lab11/buckler/software/apps/analog_accelerometer/README.md

Analog Accelerometer App
========================

Reads data from the [ADXL327](http://www.analog.com/media/en/technical-documentation/data-sheets/ADXL327.pdf)
analog accelerometer. To see output run `make rtt`

nRF SAADC (Successive Approximation Analog to Digital Converter) [API documentation]( https://infocenter.nordicsemi.com/index.jsp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)
