lab11/buckler/software/apps/blink/README.md

Blink
=====

Blinks the LEDs on Buckler

nRF GPIOTE (General Purpose I/O Task/Event) [API documentation](https://infocenter.nordicsemi.com/topic/com.nordic.infocenter.sdk5.v15.1.0/group__nrfx__gpiote.html)
