lab11/buckler/software/apps/sd_card/README.md

SD Card
=======

Writes sample lines to the SD card on Buckler
