lab11/buckler/software/apps/kobukiSquareIMU/README.md

Kobuki Square IMU
=================

Make the [Kobuki](http://kobuki.yujinrobot.com/wiki/online-user-guide/)
drive in a square using the external IMU on the buckler board
