lab11/buckler/software/apps/kobukiSensor/README.md

Kobuki Sensor
=============

Print all of the [Kobuki](http://kobuki.yujinrobot.com/wiki/online-user-guide/)
sensor values
