lab11/buckler/software/apps/button_and_switch/README.md

Buttons App
===========

Use a button and a switch to control LEDs
