lab11/buckler/software/apps/ble_robot_adv/states.h

/*
 * states.h
 *
 *  Created on: Sep 22, 2018
 *      Author: shromonaghosh
 */

#ifndef STATES_H_
#define STATES_H_

#include <stdio.h>

typedef enum {
    OFF=0,
    DRIVING,
} states;

#endif /* STATES_H_ */
