lab11/buckler/software/apps/ble_adv_listen_template/main.c

// BLE RX app
//
// Receives BLE advertisements with data

#include <stdbool.h>
#include <stdint.h>
#include "nrf.h"
#include "app_util.h"
#include "nrf_log.h"
#include "nrf_log_ctrl.h"
#include "nrf_log_default_backends.h"

#include "simple_ble.h"

// BLE configuration
// This is mostly irrelevant since we are scanning only
static simple_ble_config_t ble_config = {
        // BLE address is c0:98:e5:49:00:00
        .platform_id       = 0x49,    // used as 4th octet in device BLE address
        .device_id         = 0x0000,  // Last two octets of device address
        .adv_name          = "EE149", // irrelevant in this example
        .adv_interval      = MSEC_TO_UNITS(1000, UNIT_0_625_MS), // send a packet once per second (minimum is 20 ms)
        .min_conn_interval = MSEC_TO_UNITS(500, UNIT_1_25_MS), // irrelevant if advertising only
        .max_conn_interval = MSEC_TO_UNITS(1000, UNIT_1_25_MS), // irrelevant if advertising only
};
simple_ble_app_t* simple_ble_app;

void ble_evt_adv_report(ble_evt_t const* p_ble_evt) {

  ble_gap_evt_adv_report_t const* adv_report = &(p_ble_evt->evt.gap_evt.params.adv_report);
  // TODO: extract the fields we care about (Peer address and data)

  // TODO: filter on Peer address
  if (false) { // replace with condition on peer address
    // if address matches C0:98:E5:49:FF:FD, loop until we find field 0xFF
    while (1) {
      // TODO: get length of field
      // TODO: get type of field: if type is 0xFF, we found it!
      // Print the data as a string. i.e. printf("%s\n", data + offset)
      // Otherwise, skip ahead by the length of the current field
    }
  }
}

int main(void) {
  ret_code_t error_code = NRF_SUCCESS;

  // Initialize

  // initialize RTT library
  error_code = NRF_LOG_INIT(NULL);
  APP_ERROR_CHECK(error_code);
  NRF_LOG_DEFAULT_BACKENDS_INIT();
  printf("Log initialized\n");

  // Setup BLE
  // Note: simple BLE is our own library. You can find it in `nrf5x-base/lib/simple_ble/`
  simple_ble_app = simple_ble_init(&ble_config);
  advertising_stop();

  // TODO: Start scanning

  while(1) {
    // Sleep while SoftDevice handles BLE
    power_manage();
  }
}
