lab11/buckler/software/apps/virtual_timers/virtual_timer.c

// Virtual timer implementation

#include <stdbool.h>
#include <stdint.h>
#include <stdio.h>
#include <stdlib.h>

#include "nrf.h"

#include "virtual_timer.h"
#include "virtual_timer_linked_list.h"

// This is the interrupt handler that fires on a compare event
void TIMER4_IRQHandler(void) {
  // This should always be the first line of the interrupt handler!
  // It clears the event so that it doesn't happen again
  NRF_TIMER4->EVENTS_COMPARE[0] = 0;

  // Place your interrupt handler code here

}

// Read the current value of the timer counter
uint32_t read_timer(void) {

  // Should return the value of the internal counter for TIMER4
  return 0;
}

// Initialize TIMER4 as a free running timer
// 1) Set to be a 32 bit timer
// 2) Set to count at 1MHz
// 3) Enable the timer peripheral interrupt (look carefully at the INTENSET register!)
// 4) Clear the timer
// 5) Start the timer
void virtual_timer_init(void) {
  // Place your timer initialization code here
}

// Start a timer. This function is called for both one-shot and repeated timers
// To start a timer:
// 1) Create a linked list node (This requires `malloc()`. Don't forget to free later)
// 2) Setup the linked list node with the correct information
//      - You will need to modify the `node_t` struct in "virtual_timer_linked_list.h"!
// 3) Place the node in the linked list
// 4) Setup the compare register so that the timer fires at the right time
// 5) Return a timer ID
//
// Your implementation will also have to take special precautions to make sure that
//  - You do not miss any timers
//  - You do not cause consistency issues in the linked list (hint: you may need the `__disable_irq()` and `__enable_irq()` functions).
//
// Follow the lab manual and start with simple cases first, building complexity and
// testing it over time.
static uint32_t timer_start(uint32_t microseconds, virtual_timer_callback_t cb, bool repeated) {

  // Return a unique timer ID. (hint: What is guaranteed unique about the timer you have created?)
  return 0;
}

// You do not need to modify this function
// Instead, implement timer_start
uint32_t virtual_timer_start(uint32_t microseconds, virtual_timer_callback_t cb) {
  return timer_start(microseconds, cb, false);
}

// You do not need to modify this function
// Instead, implement timer_start
uint32_t virtual_timer_start_repeated(uint32_t microseconds, virtual_timer_callback_t cb) {
  return timer_start(microseconds, cb, true);
}

// Remove a timer by ID.
// Make sure you don't cause linked list consistency issues!
// Do not forget to free removed timers.
void virtual_timer_cancel(uint32_t timer_id) {
}
