lab11/buckler/software/apps/ble_adv_template/read_advertisement.py

#!/usr/bin/env python3

import struct
from bluepy.btle import ScanEntry, Scanner, DefaultDelegate
import argparse

parser = argparse.ArgumentParser(description='Print advertisement data from a BLE device')
parser.add_argument('addr', metavar='A', type=str, help='Address of the form XX:XX:XX:XX:XX:XX')
args = parser.parse_args()
addr = args.addr.lower()
if len(addr) != 17:
    raise ValueError("Invalid address supplied")

class ScanDelegate(DefaultDelegate):
    def __init__(self):
        DefaultDelegate.__init__(self)

    # when this python script discovers a BLE broadcast packet from a buckler
    # advertising light measurements, print out the data
    def handleDiscovery(self, dev, isNewDev, isNewData):
        if dev.addr == addr:
            print("Found advertisement from: ", str(dev.addr))
            print("Name: " + str(dev.getValueText(ScanEntry.COMPLETE_LOCAL_NAME)))
            data = dev.getValue(ScanEntry.MANUFACTURER)
            if data is not None:
                print("Data: " + str(data.hex()))

# create a scanner object that sends BLE broadcast packets to the ScanDelegate
scanner = Scanner().withDelegate(ScanDelegate())

# start the scanner and keep the process running
scanner.start()
while True:
    print("Still running...")
    scanner.process()
