lab11/buckler/software/apps/yakindu_counter_example/point.h

/*
 * point.h
 *
 *  Created on: Aug 14, 2018
 *      Author: shromonaghosh
 */

#ifndef POINT_H_
#define POINT_H_

#include <stdint.h>

typedef struct {
    int16_t x;
    int16_t y;
} Point;

#endif /* POINT_H_ */
